svenpetersen1965/VIC-20_Diagnostics/User Port PCB/3Dprintable Case/PCB_Rev0/label/VIC-20_Diag_UP_Label.png

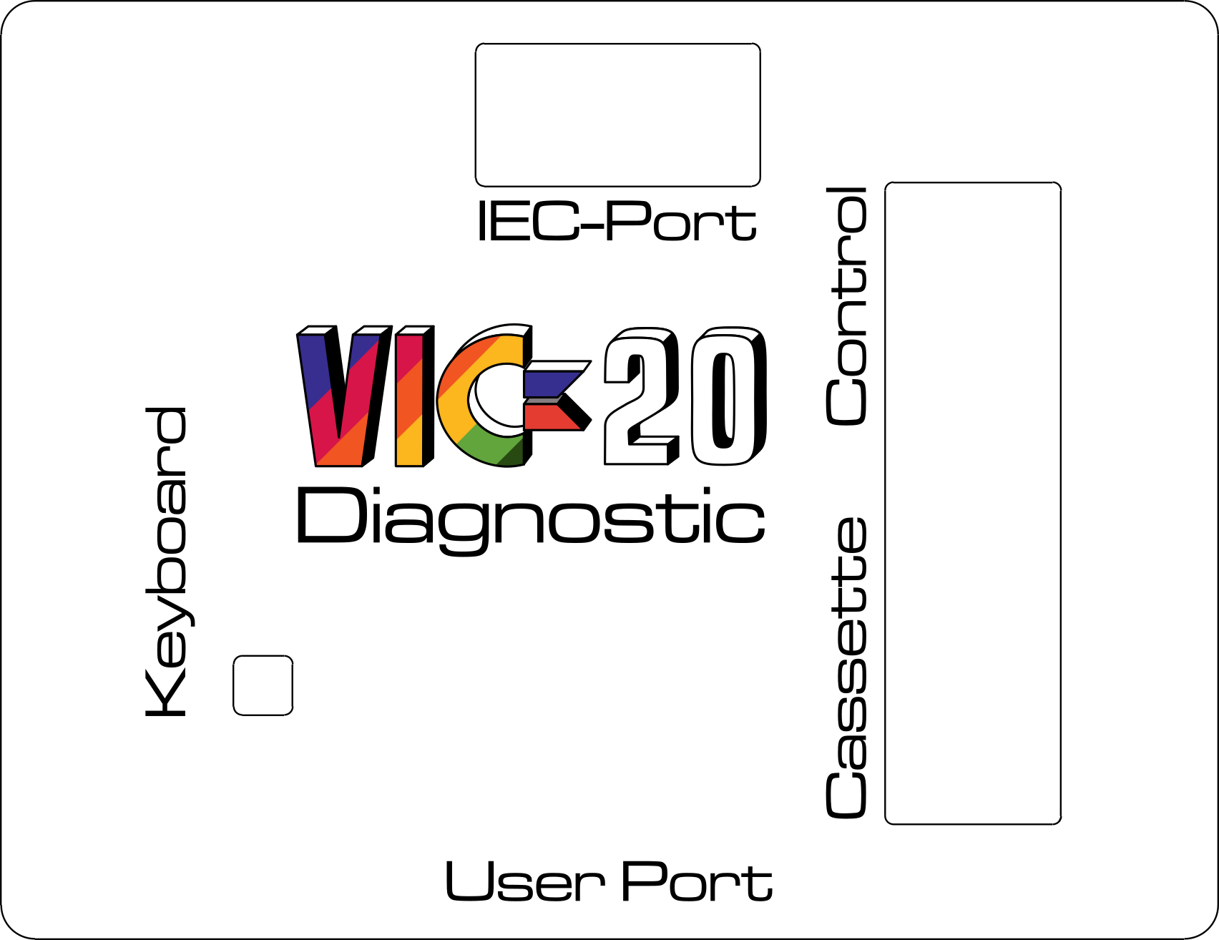
User Port PCB/3Dprintable Case/PCB_Rev0/label/VIC-20_Diag_UP_Label.png
